taunoe/s6rmlaud/img/connecting_wires_1.jpg

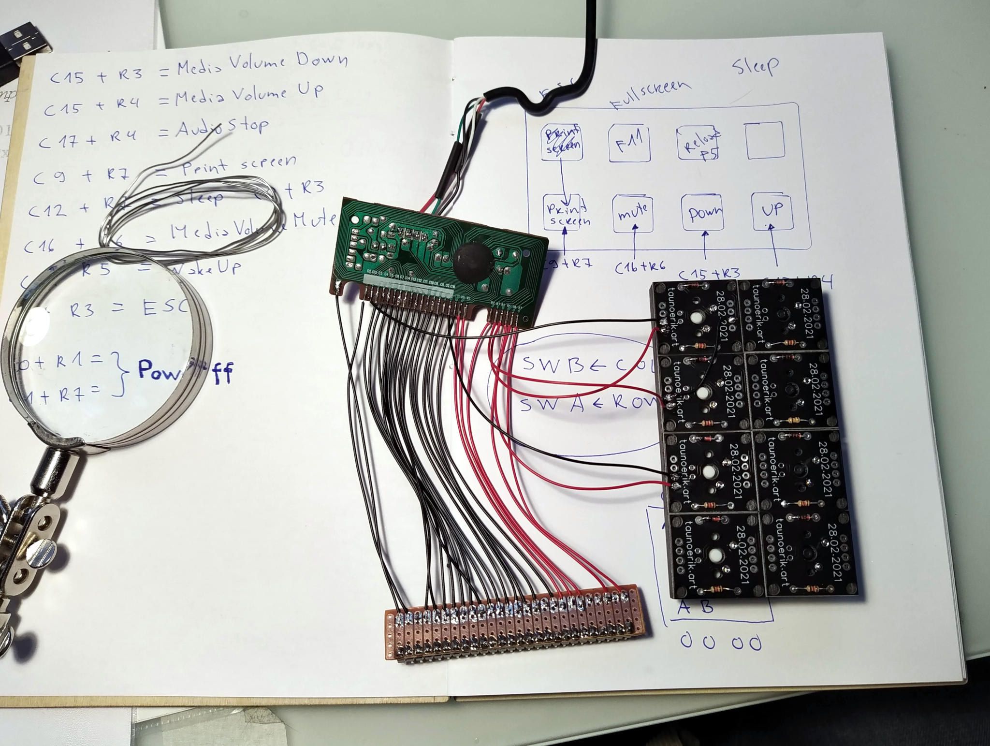
img/connecting_wires_1.jpg
