taunoe/s6rmlaud/img/connecting_wires_2.jpg

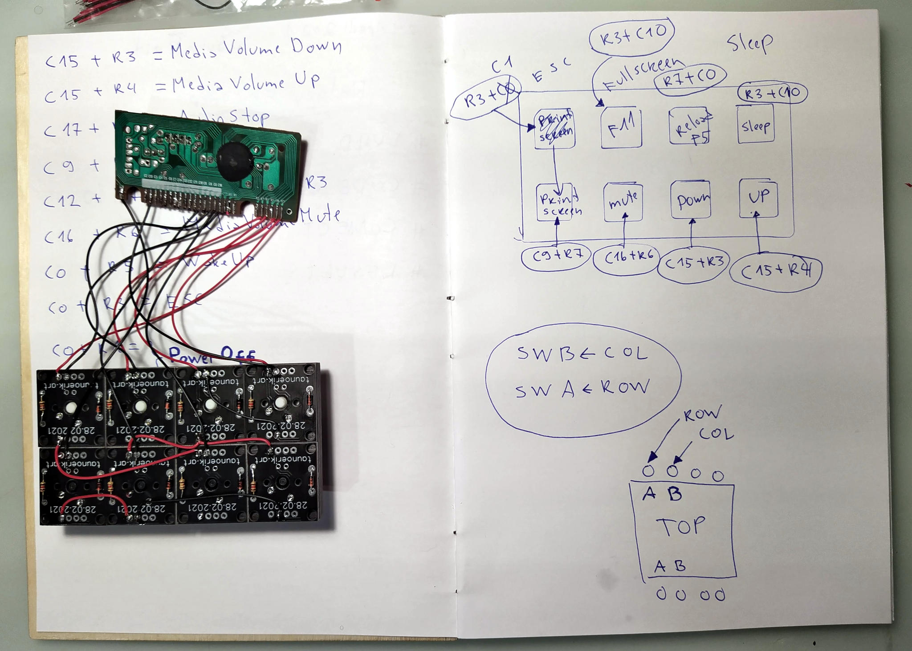
img/connecting_wires_2.jpg
