taunoe/s6rmlaud/img/IMG_8448.jpg

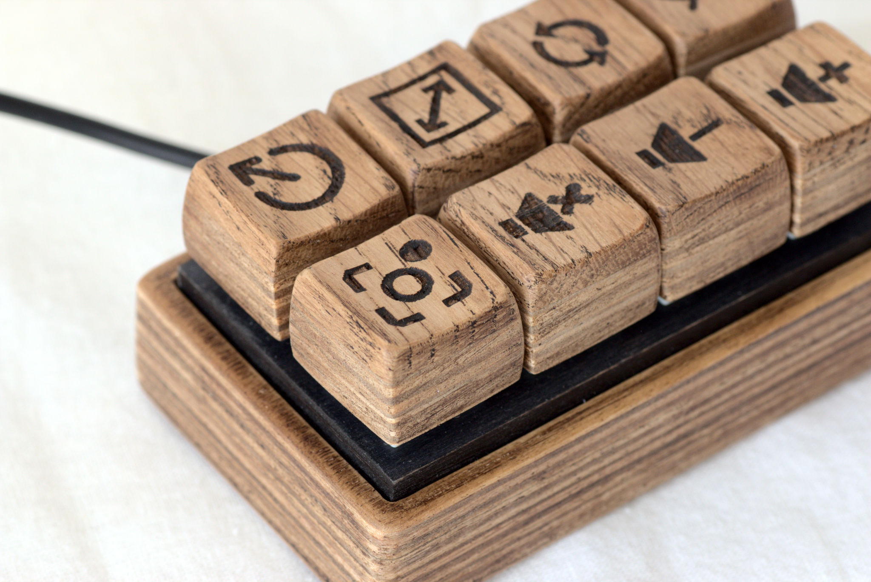
img/IMG_8448.jpg
