taunoe/s6rmlaud/img/IMG_8450.jpg

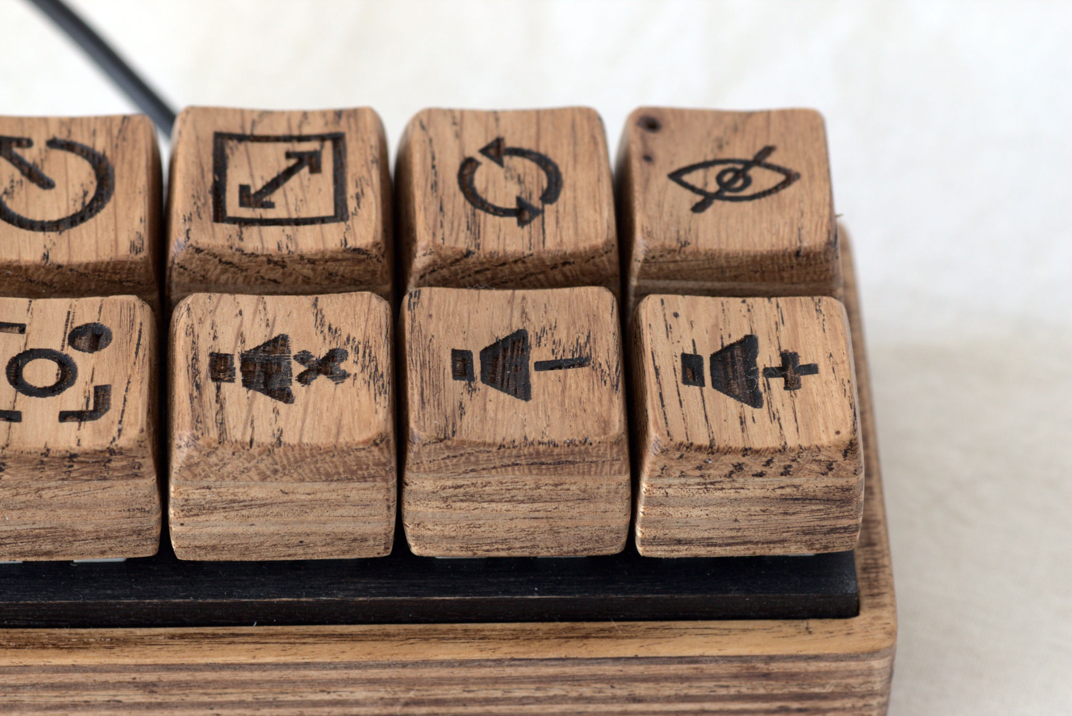
img/IMG_8450.jpg
