taunoe/s6rmlaud/img/IMG_8465.jpg

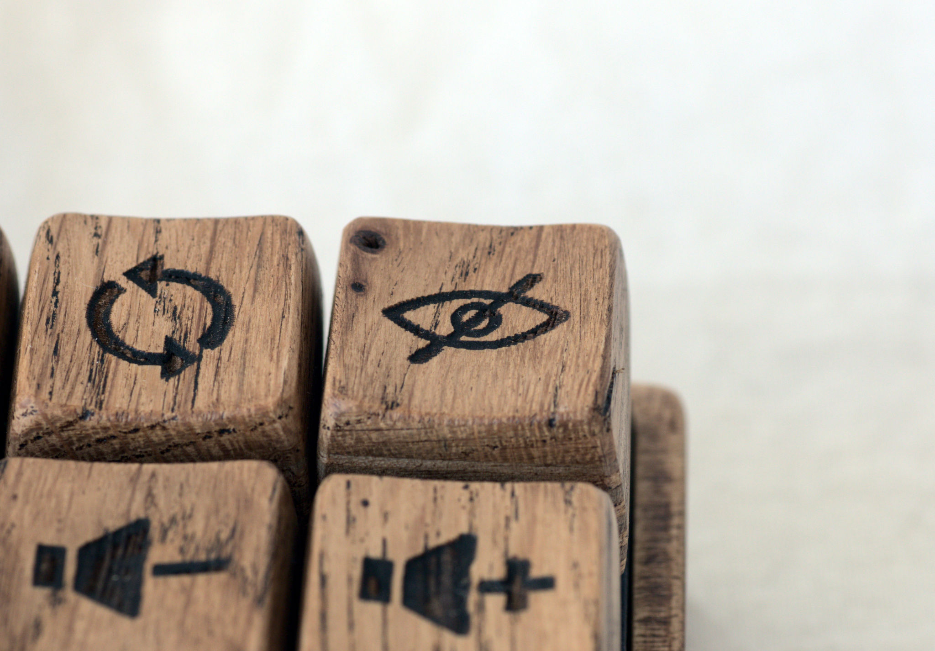
img/IMG_8465.jpg
