taunoe/s6rmlaud/img/IMG_8466.jpg

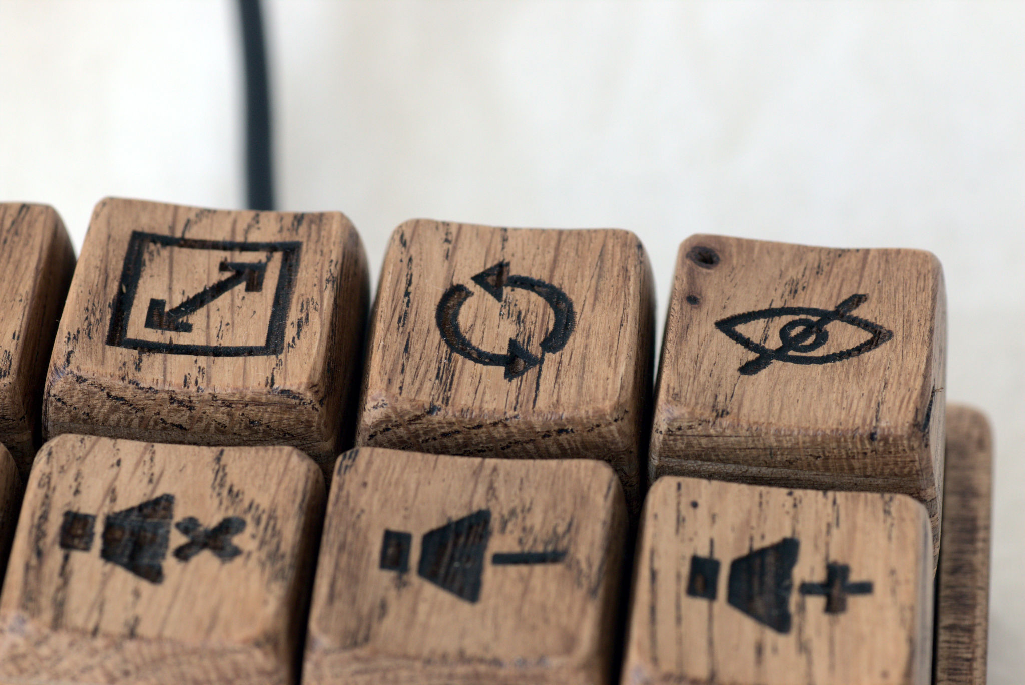
img/IMG_8466.jpg
