taunoe/s6rmlaud/img/IMG_8470.jpg

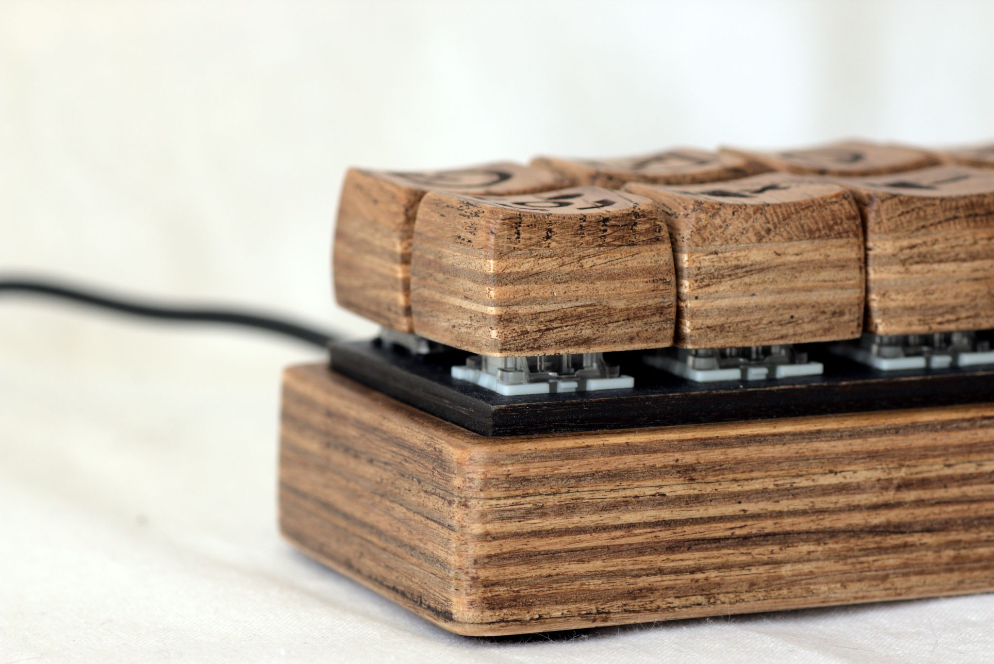
img/IMG_8470.jpg
