taunoe/s6rmlaud/img/IMG_8499.jpg

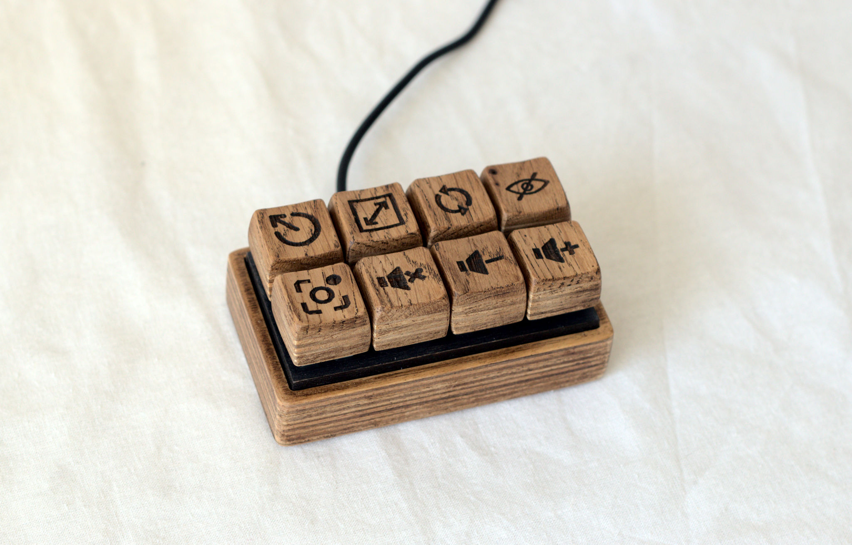
img/IMG_8499.jpg
