taunoe/s6rmlaud/img/IMG_8501.jpg

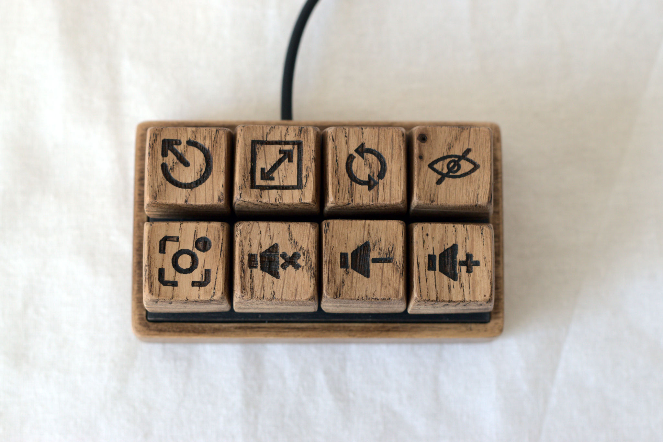
img/IMG_8501.jpg
