taunoe/s6rmlaud/img/IMG_8502.jpg

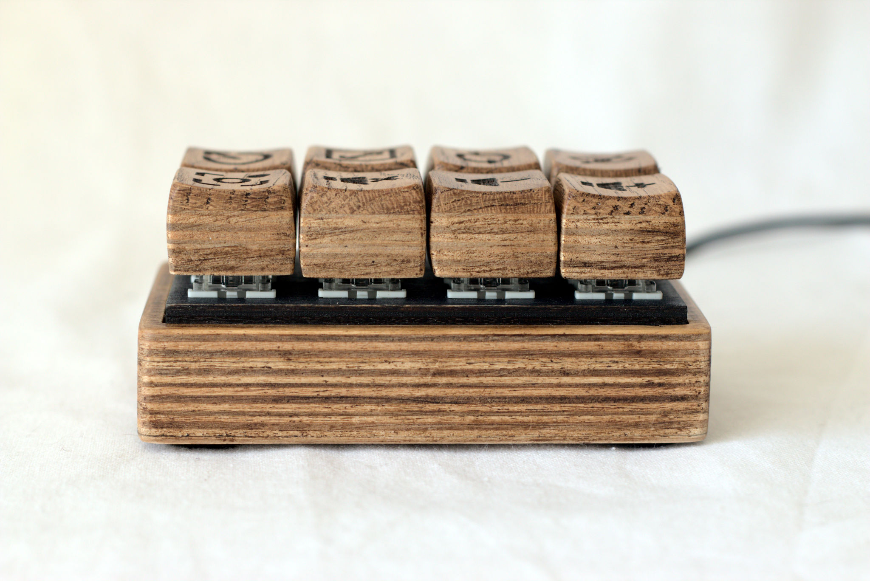
img/IMG_8502.jpg
