taunoe/s6rmlaud/img/IMG_8507.jpg

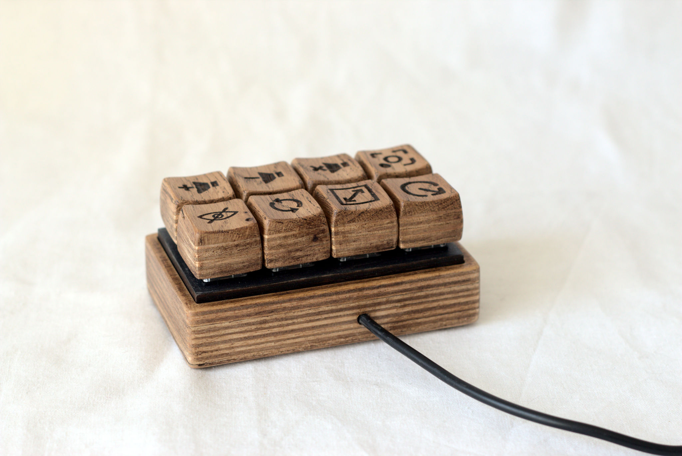
img/IMG_8507.jpg
