taunoe/s6rmlaud/img/keycaps_1.jpg

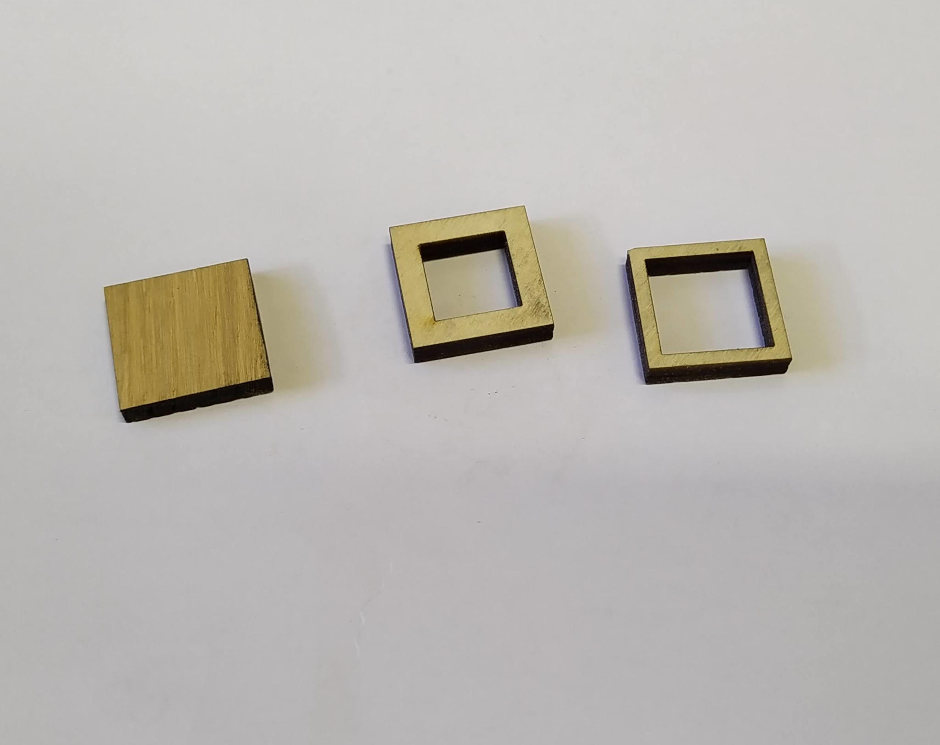
img/keycaps_1.jpg
