taunoe/s6rmlaud/img/keycaps_2.jpg

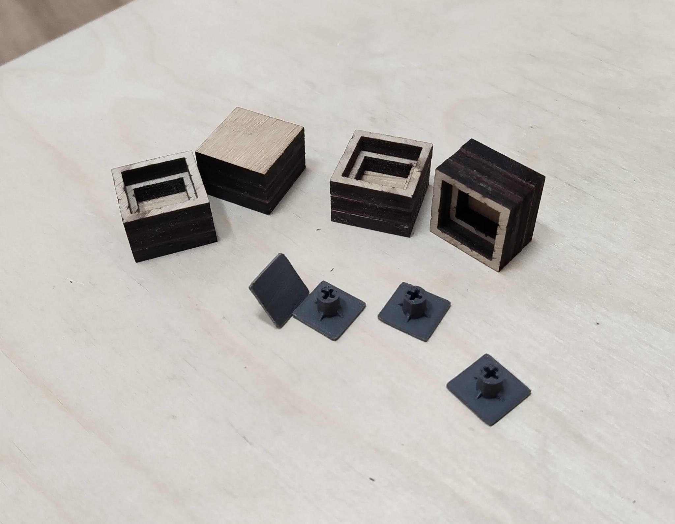
img/keycaps_2.jpg
