taunoe/s6rmlaud/img/keycaps_3.jpg

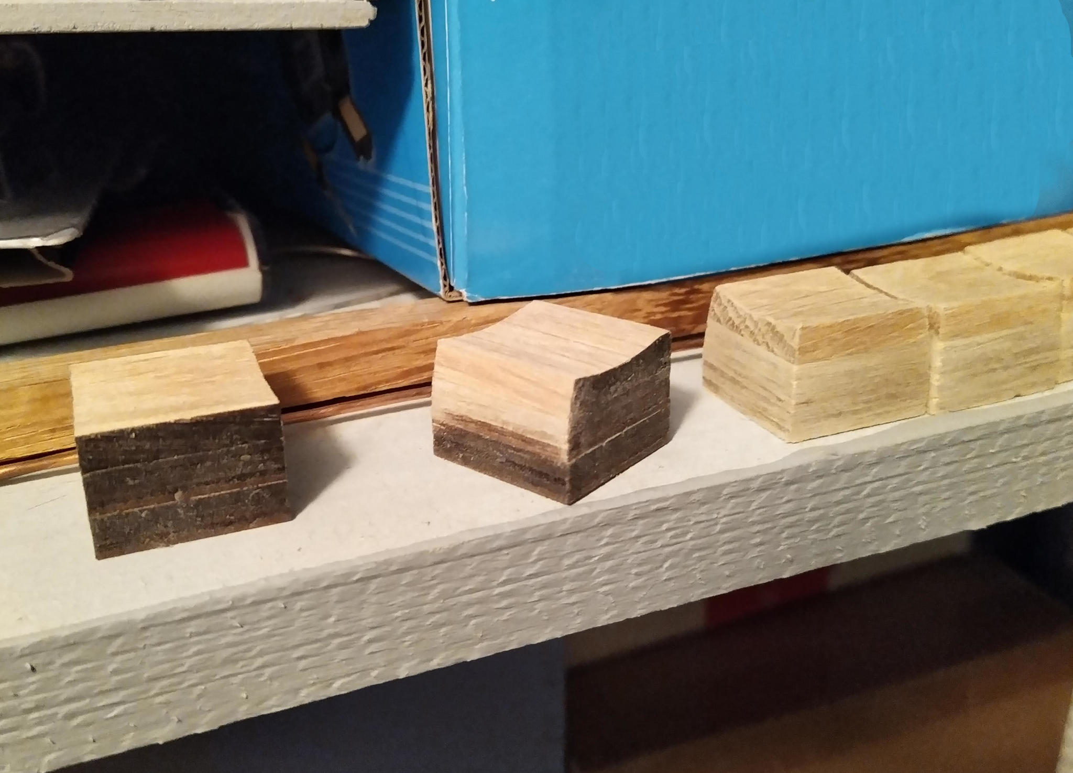
img/keycaps_3.jpg
