taunoe/s6rmlaud/img/keycaps_4.jpg

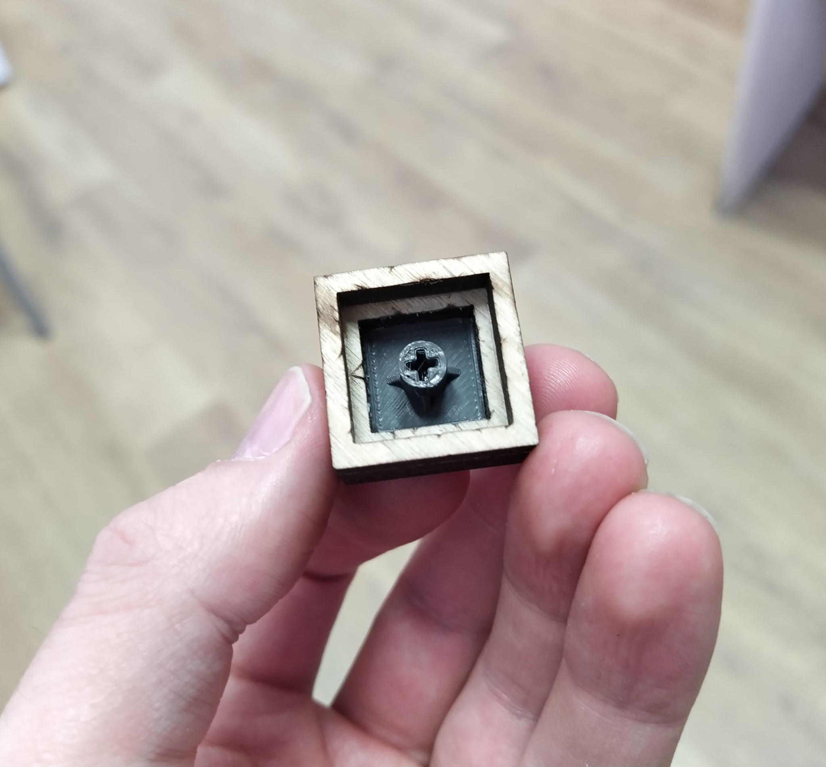
img/keycaps_4.jpg
