taunoe/s6rmlaud/img/sellecting_keys.jpg

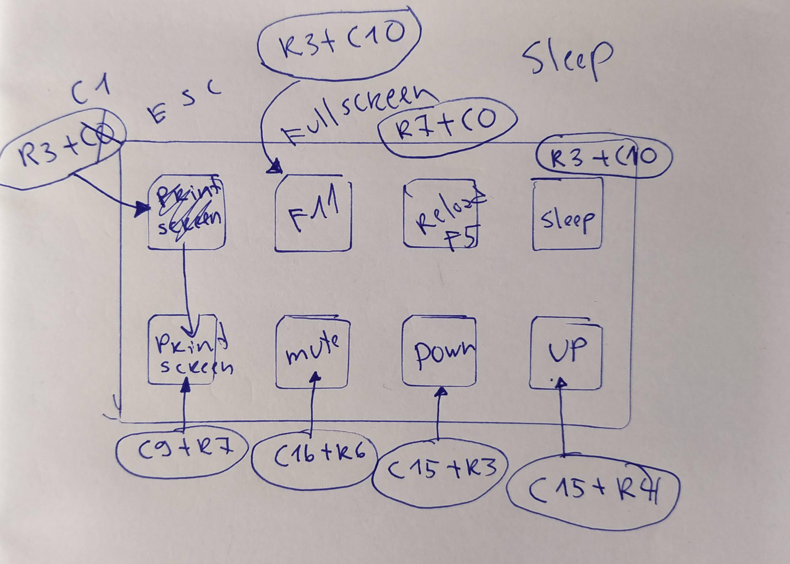
img/sellecting_keys.jpg
