taunoe/s6rmlaud/img/single_key_pcb.jpg

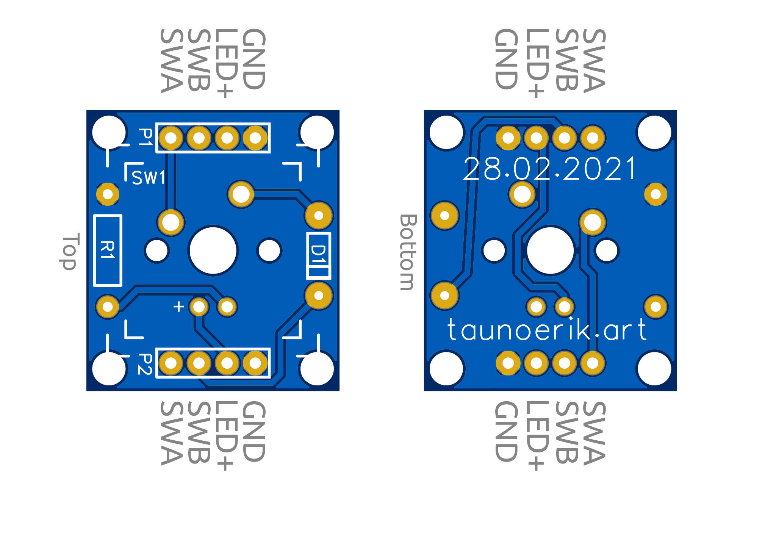
img/single_key_pcb.jpg
