taunoe/s6rmlaud/img/single_key_psb.png

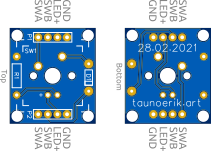
img/single_key_psb.png
