taunoe/s6rmlaud/tools/Ekraanipilt 2021-04-02 21-00-04.png

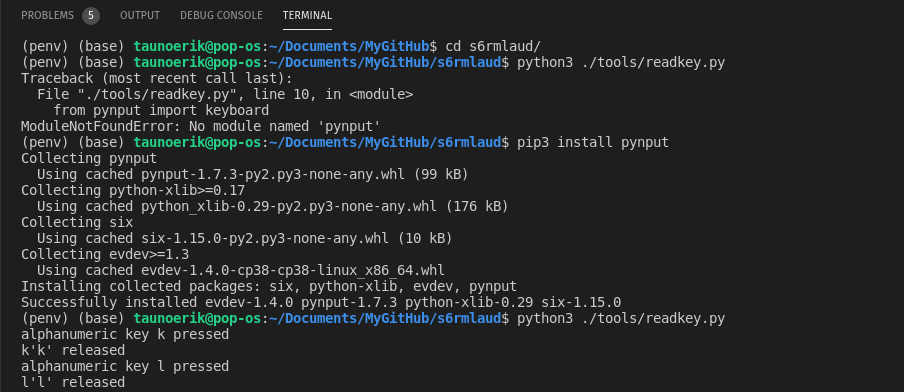
tools/Ekraanipilt 2021-04-02 21-00-04.png
