taunoe/s6rmlaud/img/assembly_2.jpg

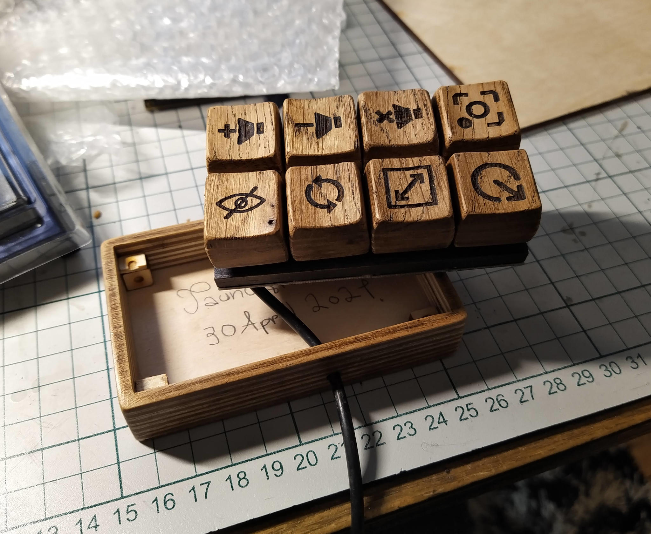
img/assembly_2.jpg
