taunoe/s6rmlaud/img/wires_and_testing.jpg

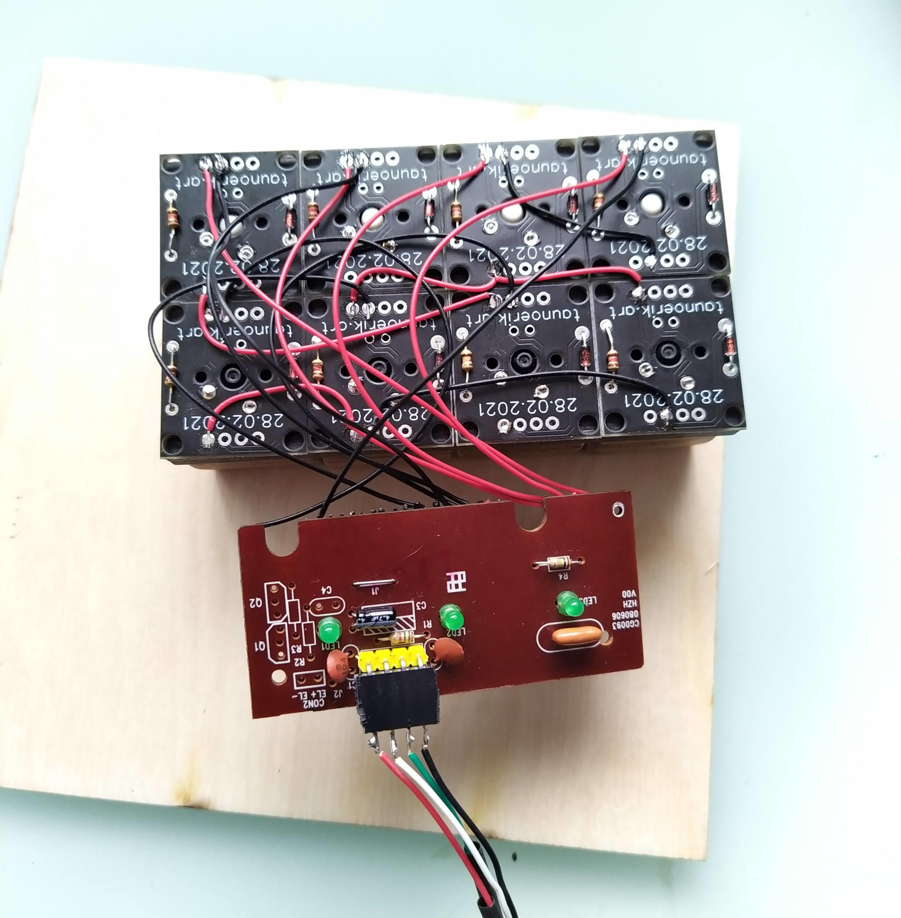
img/wires_and_testing.jpg
